halacs/hikvision-infra-panel/DS-2CD2132-I/docs/IMG20240821143729.jpg

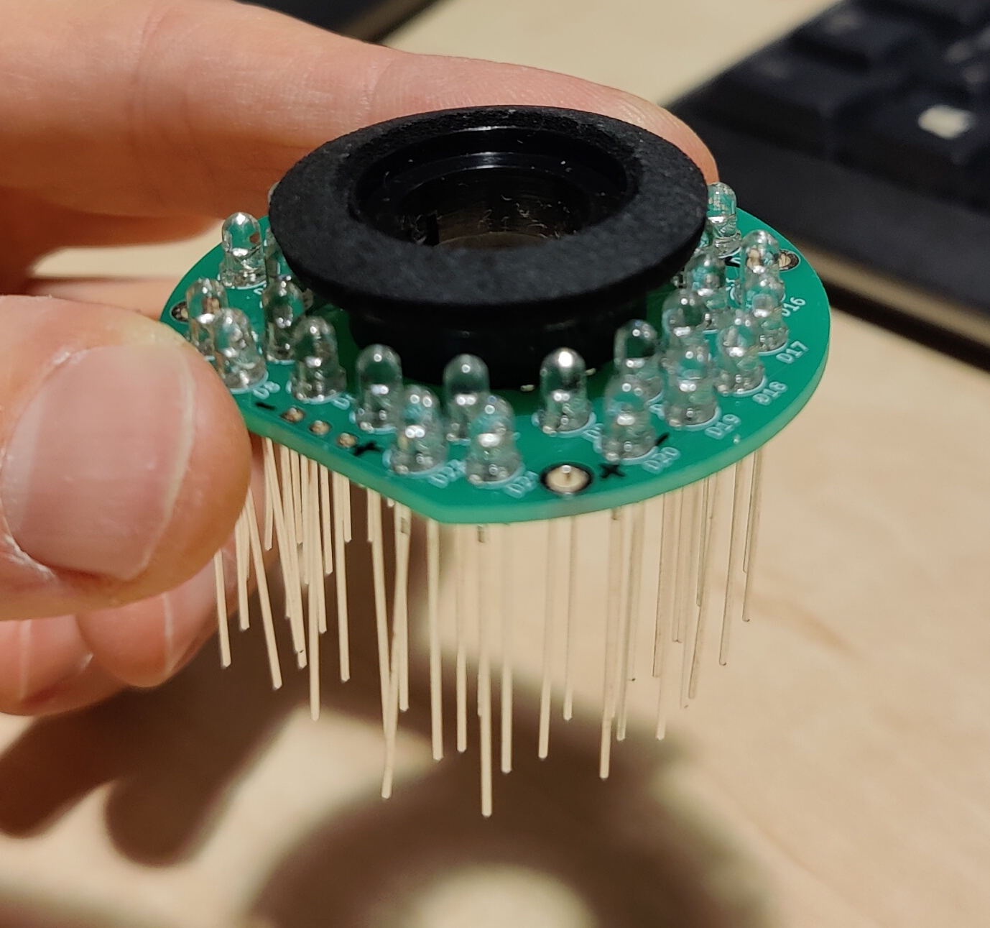
DS-2CD2132-I/docs/IMG20240821143729.jpg
